amberisvibin/chibi-pc09/docs/design notes/BR_Z800001.jpg

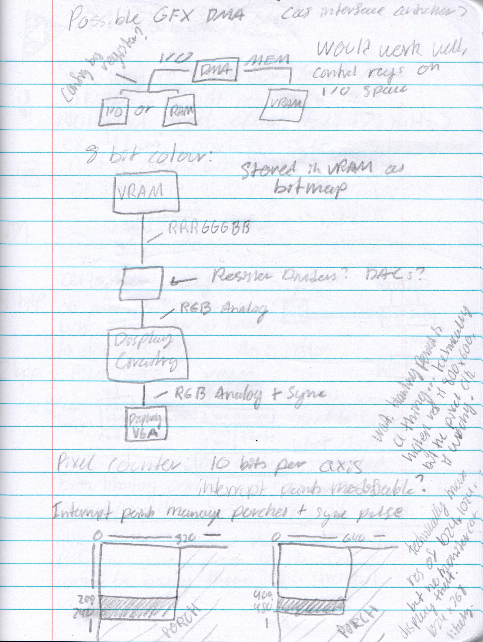
docs/design notes/BR_Z800001.jpg
