amberisvibin/chibi-pc09/docs/design notes/BR_Z800003.jpg

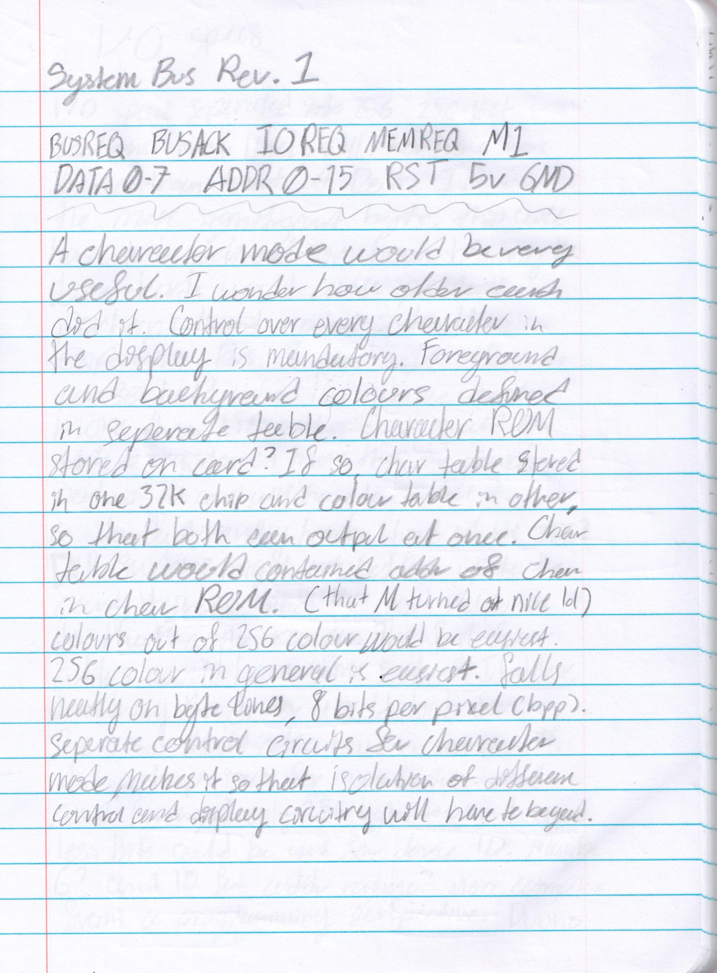
docs/design notes/BR_Z800003.jpg
