amberisvibin/chibi-pc09/pcb/prototype-1/photos/pcbproto.png

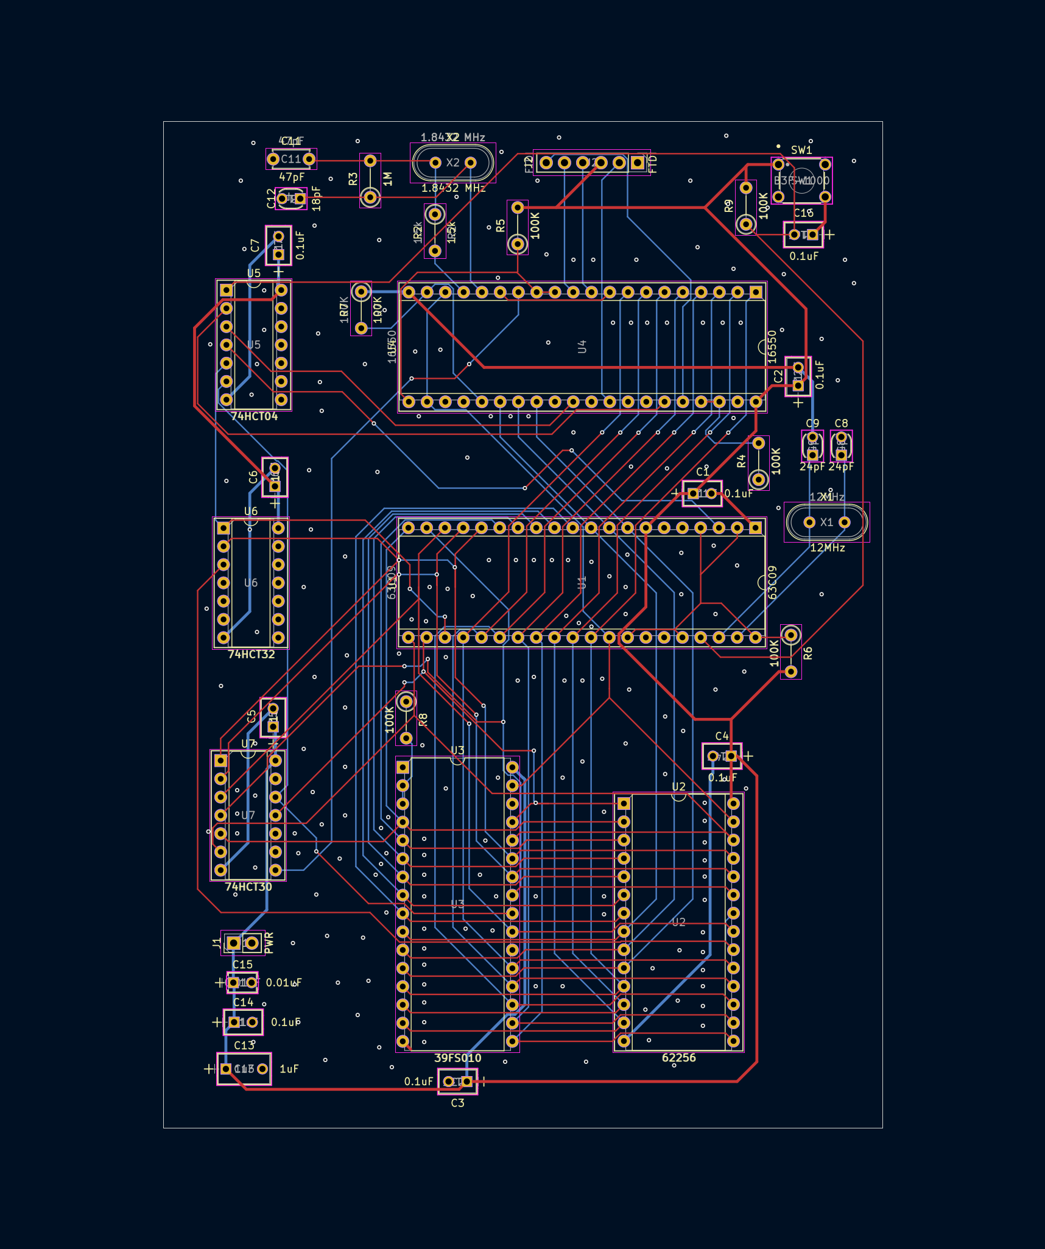
pcb/prototype-1/photos/pcbproto.png
