amberisvibin/chibi-pc09/pcb/prototype-1/photos/proto1.png

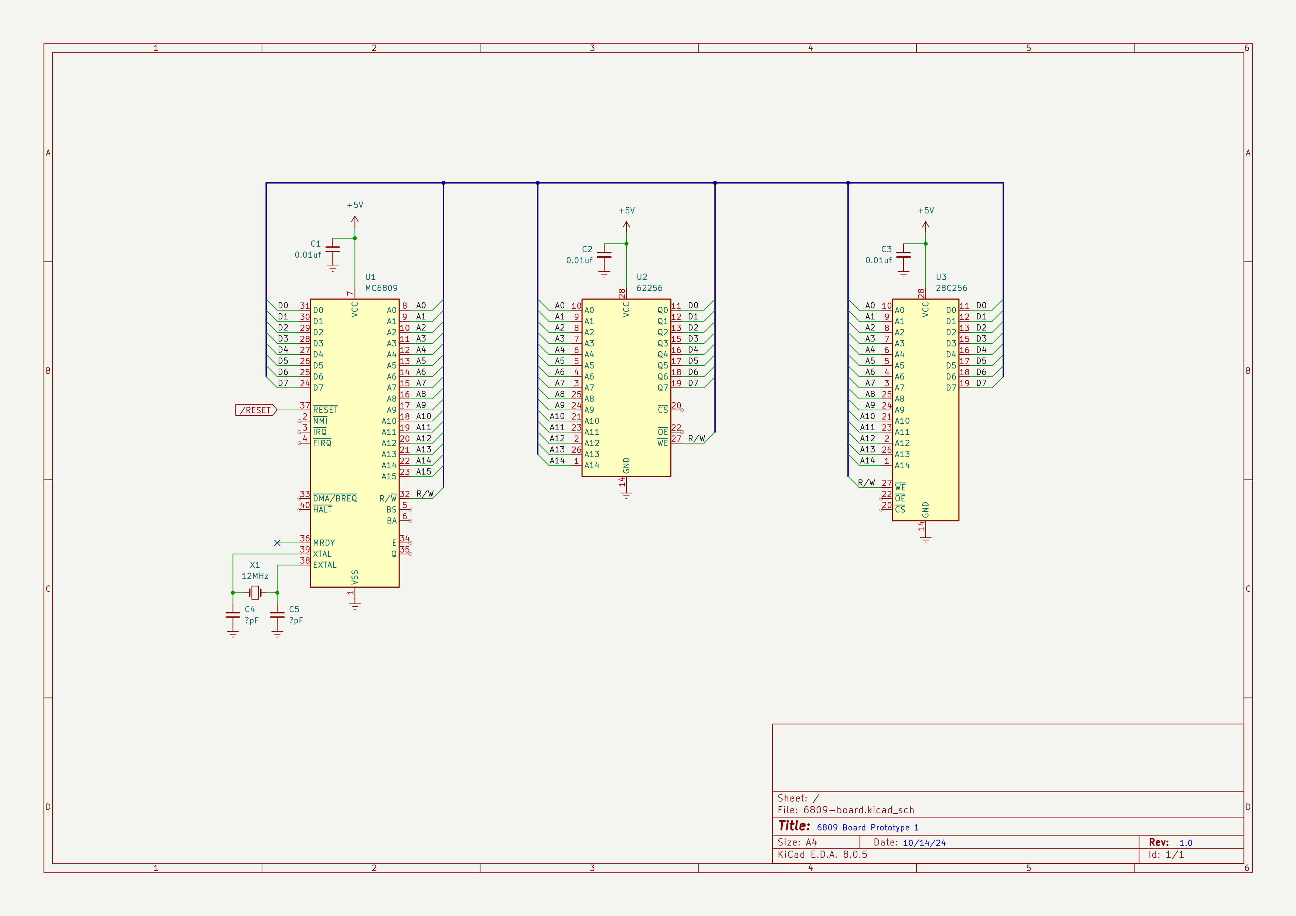
pcb/prototype-1/photos/proto1.png
