amberisvibin/chibi-pc09/pcb/prototype-1/photos/proto2.png

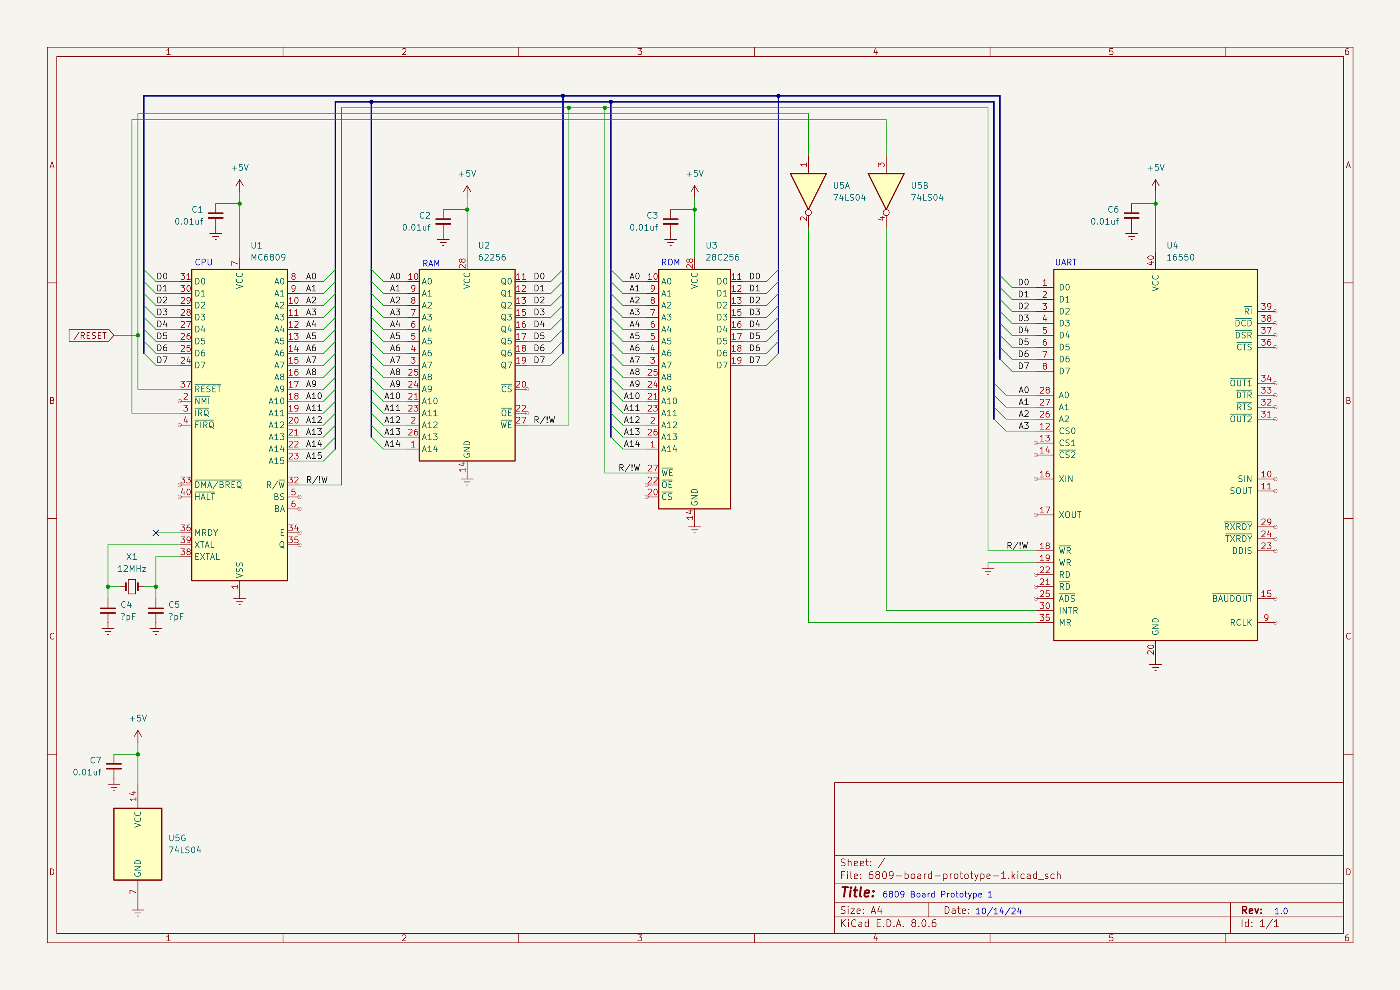
pcb/prototype-1/photos/proto2.png
