amberisvibin/chibi-pc09/pcb/prototype-1/photos/proto3.png

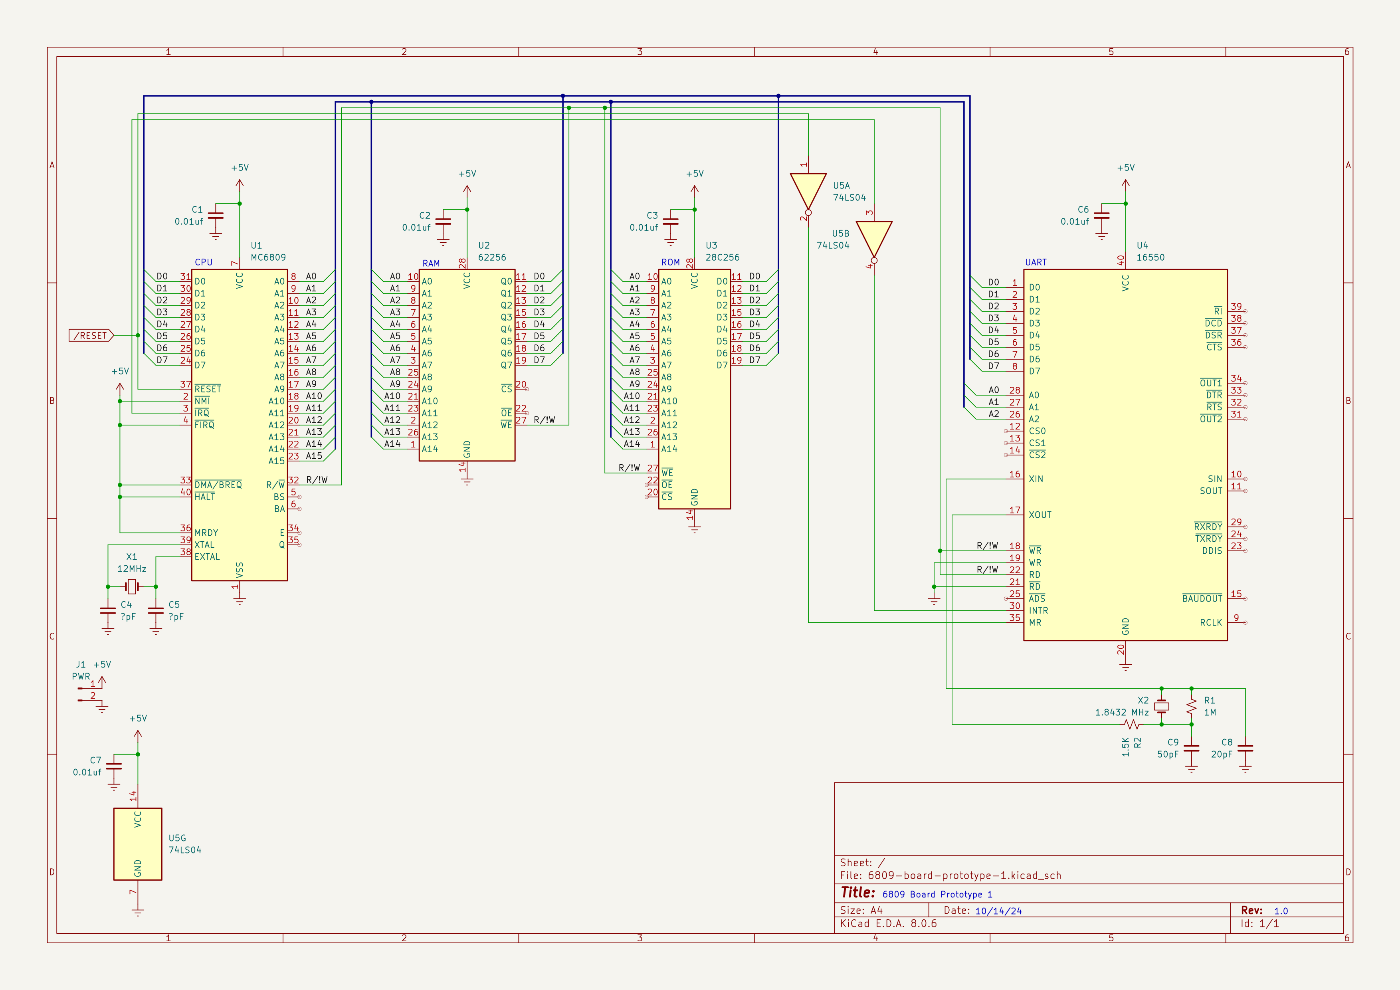
pcb/prototype-1/photos/proto3.png
