amberisvibin/chibi-pc09/pcb/prototype-1/photos/proto4.png

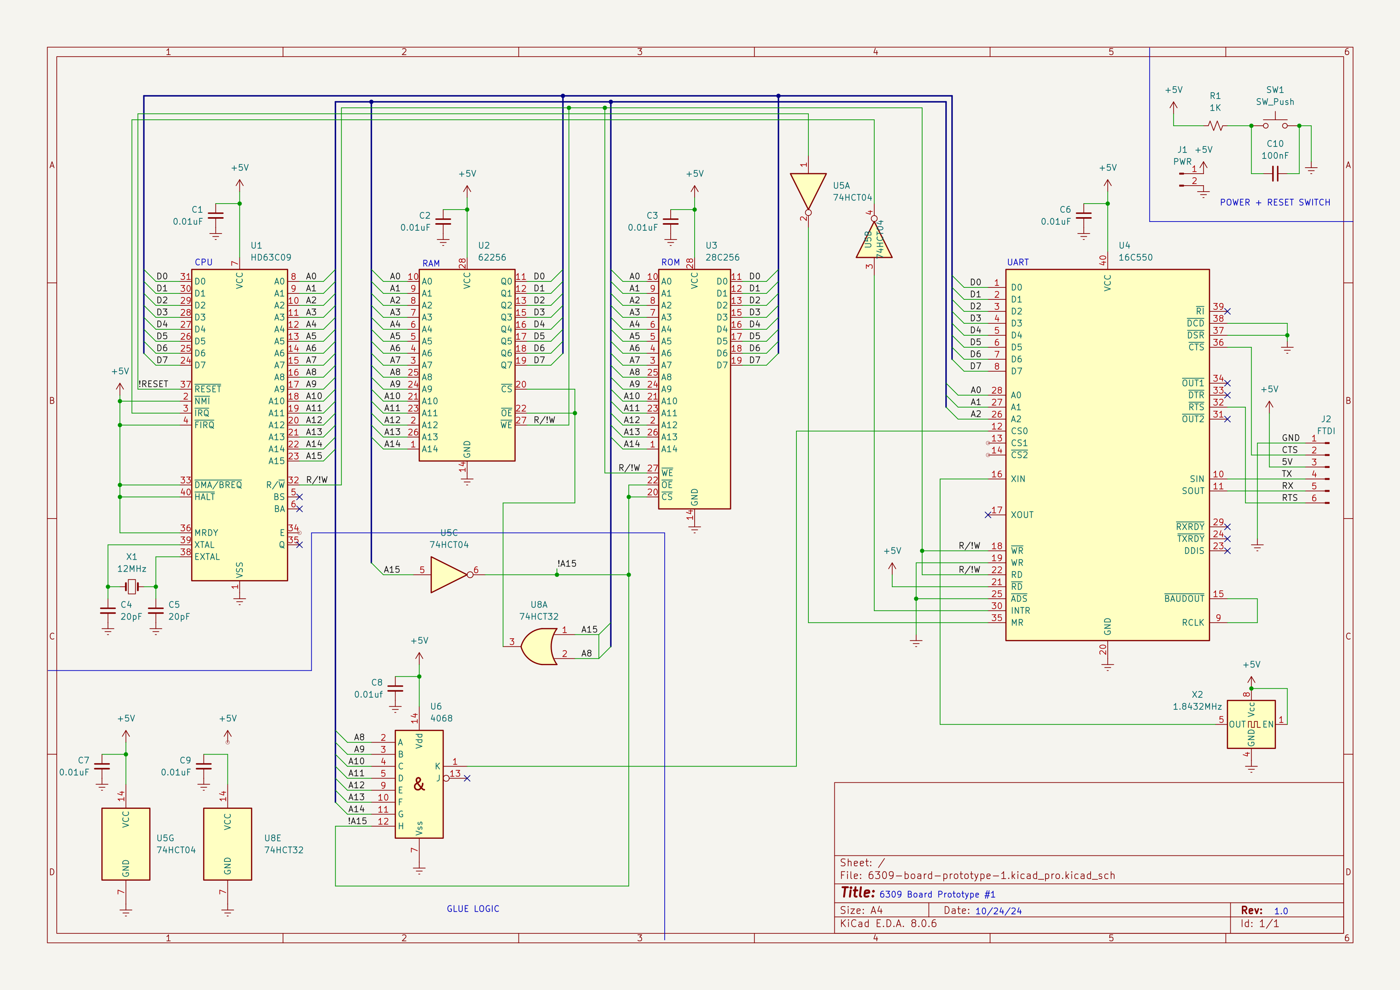
pcb/prototype-1/photos/proto4.png
