amberisvibin/chibi-pc09/pcb/prototype-1/photos/proto6.png

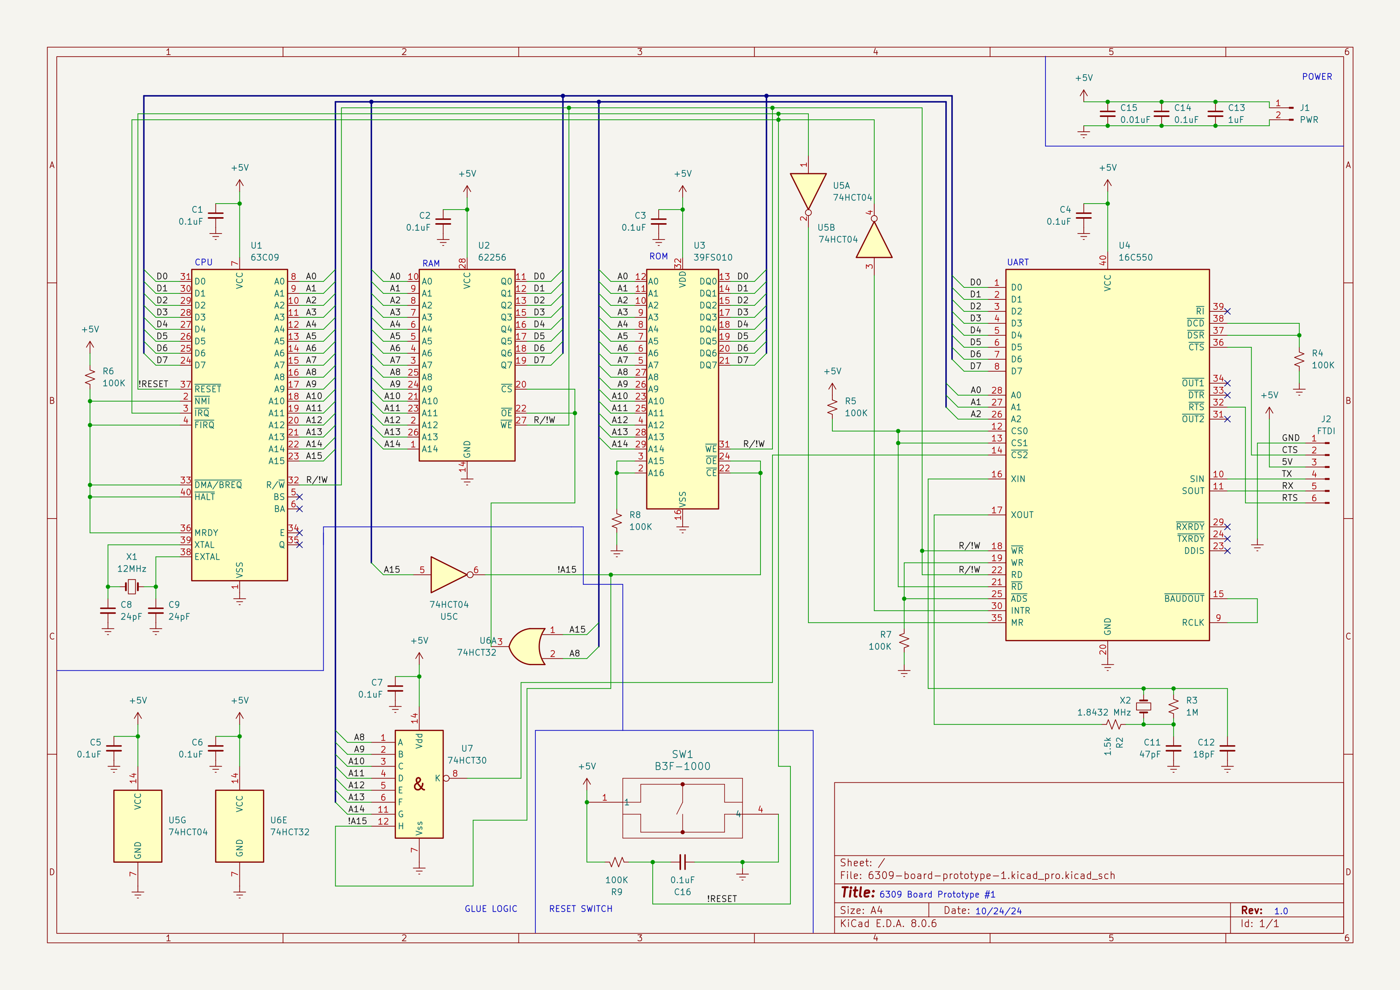
pcb/prototype-1/photos/proto6.png
