amberisvibin/chibi-pc09/6809-board-prototype-1/6809-board-prototype-1.kicad_sch

## KiCad design 6809-board-prototype-1/6809-board-prototype-1.kicad_sch (2024-10-23)

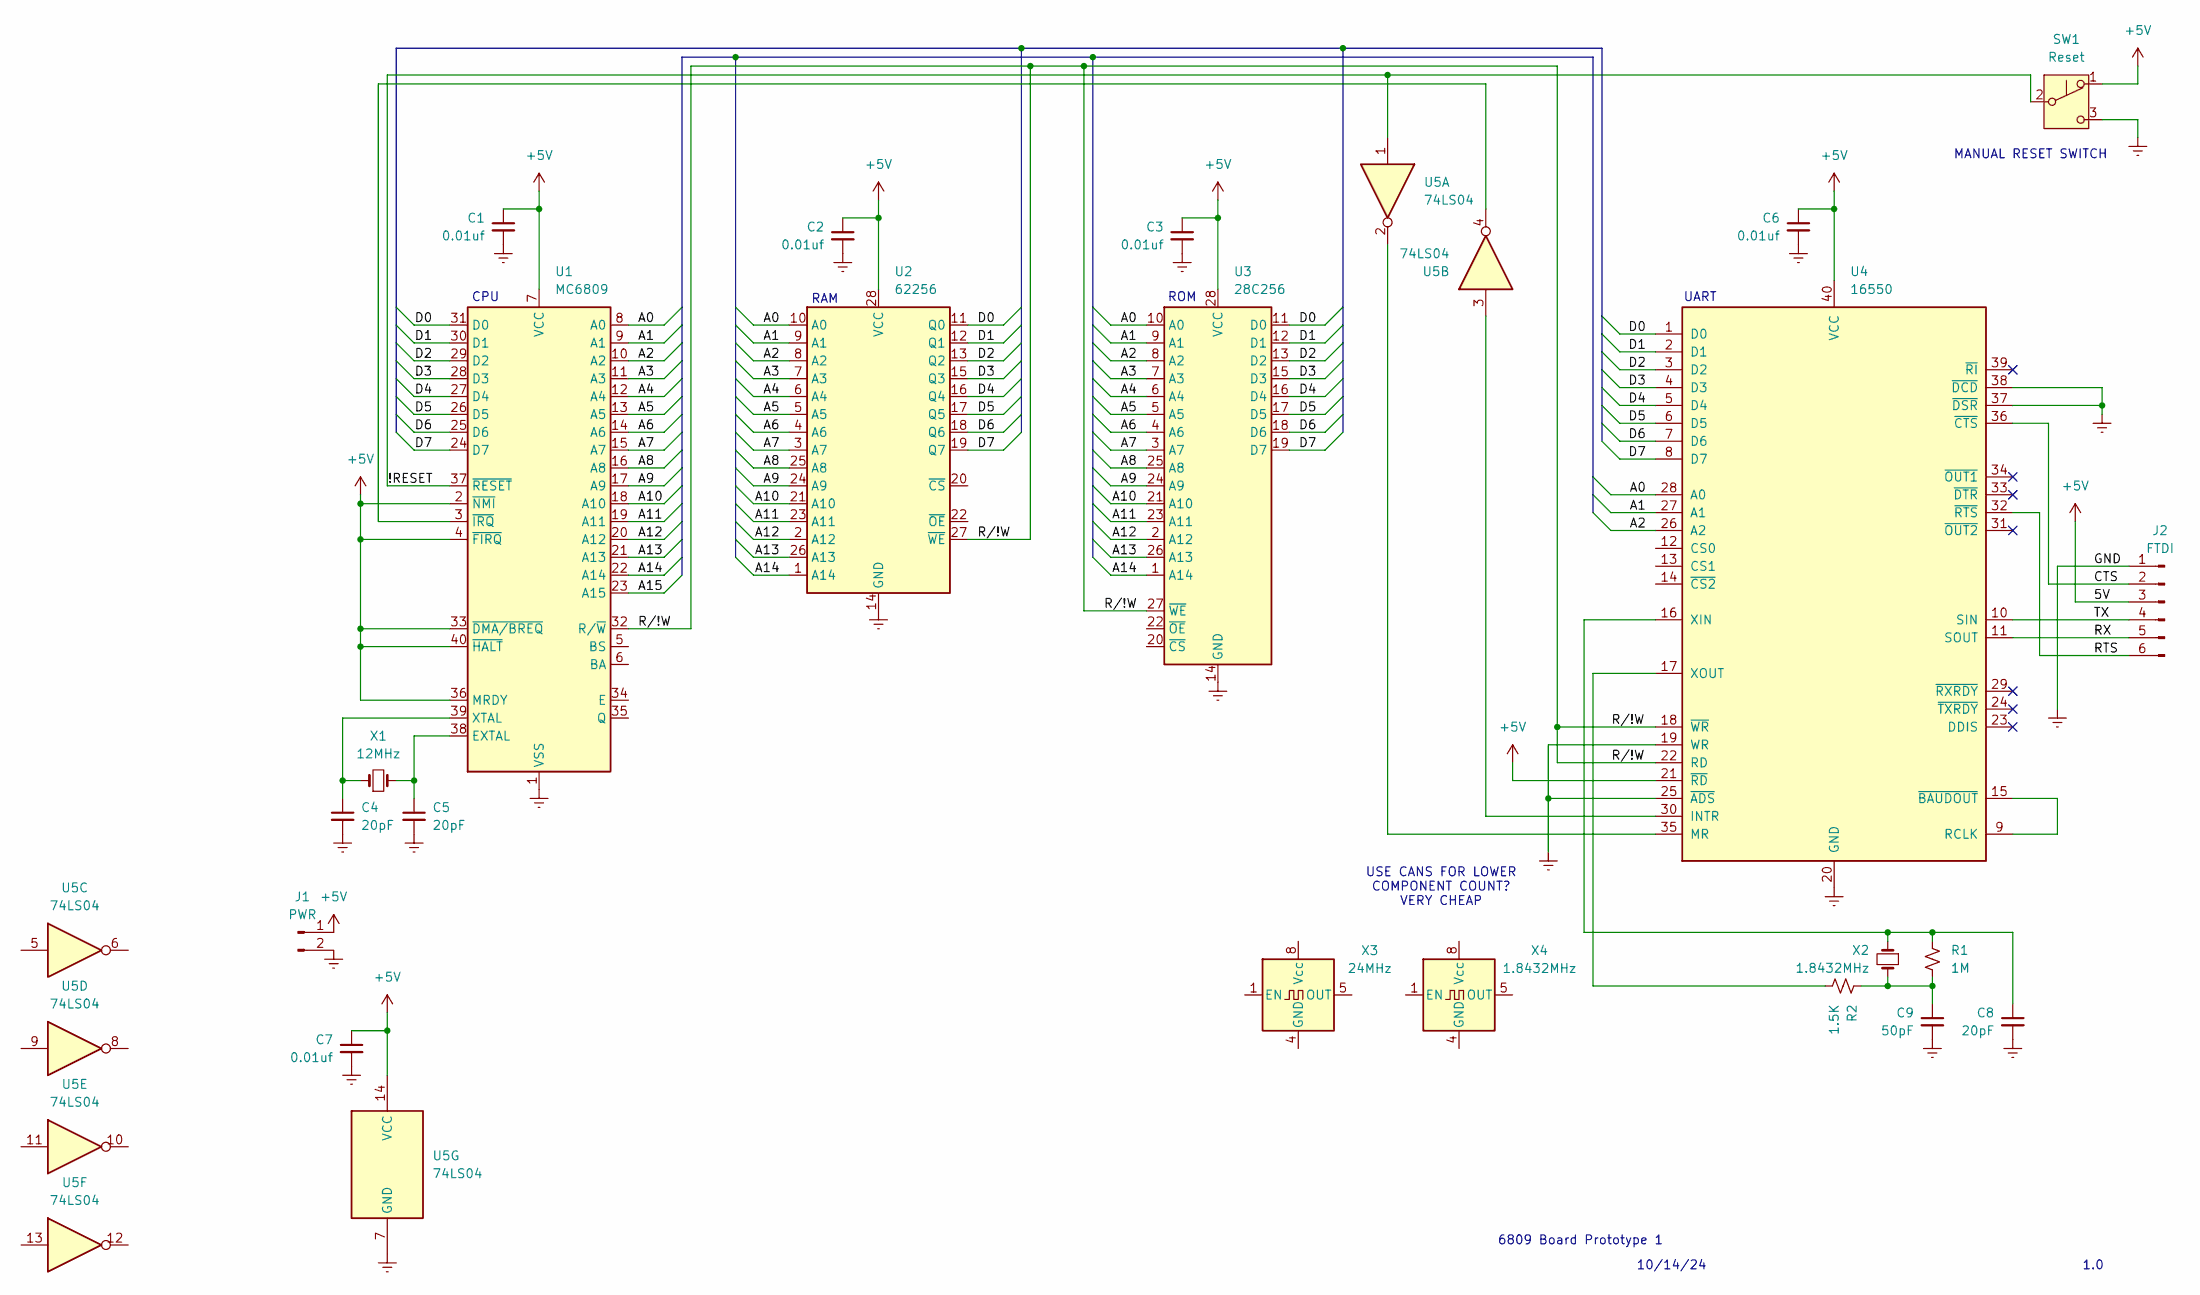
[picture p24: schematic 6809-board-prototype-1.kicad_sch]

Parts:
C1, C2, C3, C6, C7: 0.01uf
C4, C5, C8: 20pF
C9: 50pF
J1: PWR
J2: FTDI
R1: 1M
R2: 1.5K
SW1: Reset
U1: MC6809; DIP-40_W15.24mm
U2: 62256; DIP-28_W15.24mm
U3: 28C256
U4: 16550; DIP-40_W15.24mm
U5: 74LS04
X1: 12MHz
X2: 1.8432MHz
X3: 24MHz; Oscillator_DIP-8
X4: 1.8432MHz; Oscillator_DIP-8

Connections:
!RESET: SW1.2 (B), U1.37 (~RESET), U5.1
+5V: C1.1, C2.1, C3.1, C6.1, C7.1, J1.1, J2.3, SW1.1 (A), U1.2 (~NMI), U1.4 (~FIRQ), U1.7 (VCC), U1.33 (~DMA/BREQ), U1.36 (MRDY), U1.40 (~HALT), U2.28 (VCC), U3.28 (VCC), U4.21 (~RD), U4.40 (VCC), U5.14 (VCC)
A0: U1.8 (A0), U2.10 (A0), U3.10 (A0), U4.28 (A0)
A1: U1.9 (A1), U2.9 (A1), U3.9 (A1), U4.27 (A1)
A2: U1.10 (A2), U2.8 (A2), U3.8 (A2), U4.26 (A2)
A3: U1.11 (A3), U2.7 (A3), U3.7 (A3)
A4: U1.12 (A4), U2.6 (A4), U3.6 (A4)
A5: U1.13 (A5), U2.5 (A5), U3.5 (A5)
A6: U1.14 (A6), U2.4 (A6), U3.4 (A6)
A7: U1.15 (A7), U2.3 (A7), U3.3 (A7)
A8: U1.16 (A8), U2.25 (A8), U3.25 (A8)
A9: U1.17 (A9), U2.24 (A9), U3.24 (A9)
A10: U1.18 (A10), U2.21 (A10), U3.21 (A10)
A11: U1.19 (A11), U2.23 (A11), U3.23 (A11)
A12: U1.20 (A12), U2.2 (A12), U3.2 (A12)
A13: U1.21 (A13), U2.26 (A13), U3.26 (A13)
A14: U1.22 (A14), U2.1 (A14), U3.1 (A14)
A15: U1.23 (A15)
CTS: J2.2, U4.36 (~CTS)
D0: U1.31 (D0), U2.11 (Q0), U3.11 (D0), U4.1 (D0)
D1: U1.30 (D1), U2.12 (Q1), U3.12 (D1), U4.2 (D1)
D2: U1.29 (D2), U2.13 (Q2), U3.13 (D2), U4.3 (D2)
D3: U1.28 (D3), U2.15 (Q3), U3.15 (D3), U4.4 (D3)
D4: U1.27 (D4), U2.16 (Q4), U3.16 (D4), U4.5 (D4)
D5: U1.26 (D5), U2.17 (Q5), U3.17 (D5), U4.6 (D5)
D6: U1.25 (D6), U2.18 (Q6), U3.18 (D6), U4.7 (D6)
D7: U1.24 (D7), U2.19 (Q7), U3.19 (D7), U4.8 (D7)
GND: C1.2, C2.2, C3.2, C4.2, C5.2, C6.2, C7.2, C8.2, C9.2, J1.2, J2.1, SW1.3 (C), U1.1 (VSS), U2.14 (GND), U3.14 (GND), U4.19 (WR), U4.20 (GND), U4.25 (~ADS), U4.37 (~DSR), U4.38 (~DCD), U5.7 (GND)
unnamed: C4.1, U1.39 (XTAL), X1.1
unnamed: C5.1, U1.38 (EXTAL), X1.2
unnamed: C8.1, R1.1, U4.16 (XIN), X2.1
unnamed: C9.1, R1.2, R2.1, X2.2
unnamed: R2.2, U4.17 (XOUT)
unnamed: U1.3 (~IRQ), U5.4
unnamed: U4.9 (RCLK), U4.15 (~BAUDOUT)
unnamed: U4.30 (INTR), U5.3
unnamed: U4.35 (MR), U5.2
RTS: J2.6, U4.32 (~RTS)
RX: J2.5, U4.11 (SOUT)
R/!W: U1.32 (R/~W), U2.27 (~WE), U3.27 (~WE), U4.18 (~WR), U4.22 (RD)
TX: J2.4, U4.10 (SIN)

Notes on the sheet:
1.0
ROM
USE CANS FOR LOWER COMPONENT COUNT? VERY CHEAP
UART
CPU
MANUAL RESET SWITCH
6809 Board Prototype 1
10/14/24
RAM
